107-systems/l3xz-cad/cad/upper_deck/emergency_stop_TC-9219036.step

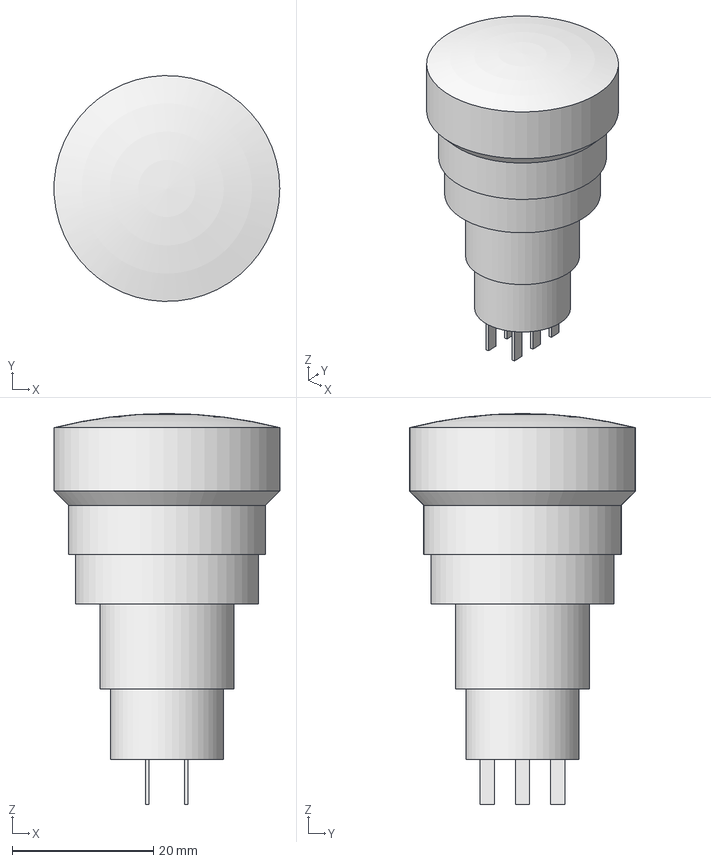
[picture p15: CAD file, 2023-01-18]
cad/upper_deck/emergency_stop_TC-9219036.step
32.0 x 32.0 x 55.4 mm
