107-systems/l3xz-cad/cad/body-bottom-middle-bracket-holes.dxf

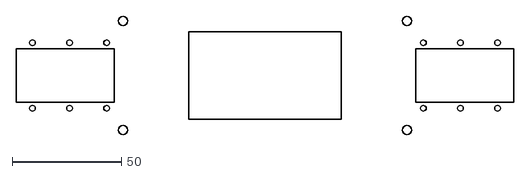
[picture p16: CAD file, 2022-04-17]
cad/body-bottom-middle-bracket-holes.dxf
228.0 x 54.3
