107-systems/l3xz-cad/cad/upper_deck/Adafruit_Neopixel.step

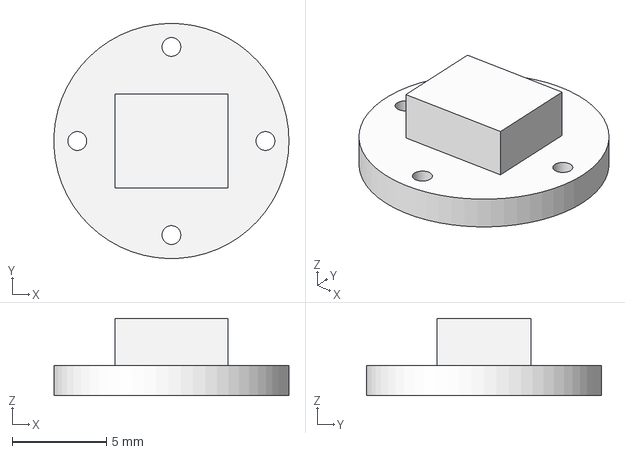
[picture p17: CAD file, 2022-05-29]
cad/upper_deck/Adafruit_Neopixel.step
12.5 x 12.5 x 4.10 mm
