107-systems/l3xz-cad/cad/middle-bracket.step

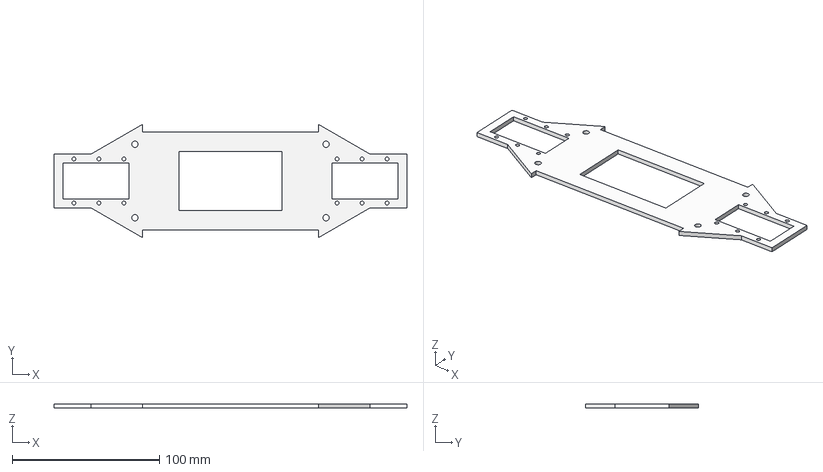
[picture p18: CAD file, 2022-04-17]
cad/middle-bracket.step
240.0 x 76.8 x 3.00 mm
