107-systems/l3xz-cad/cad/upper_deck/Scanse_Sweep_Adapter.step

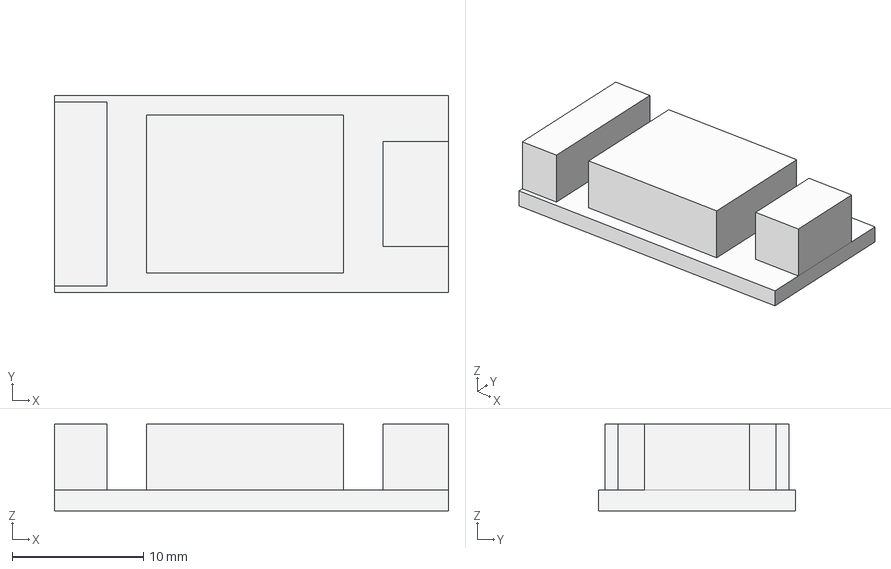
[picture p19: CAD file, 2022-05-29]
cad/upper_deck/Scanse_Sweep_Adapter.step
30.0 x 15.0 x 6.60 mm
