107-systems/l3xz-cad/cad/switch_mount.step

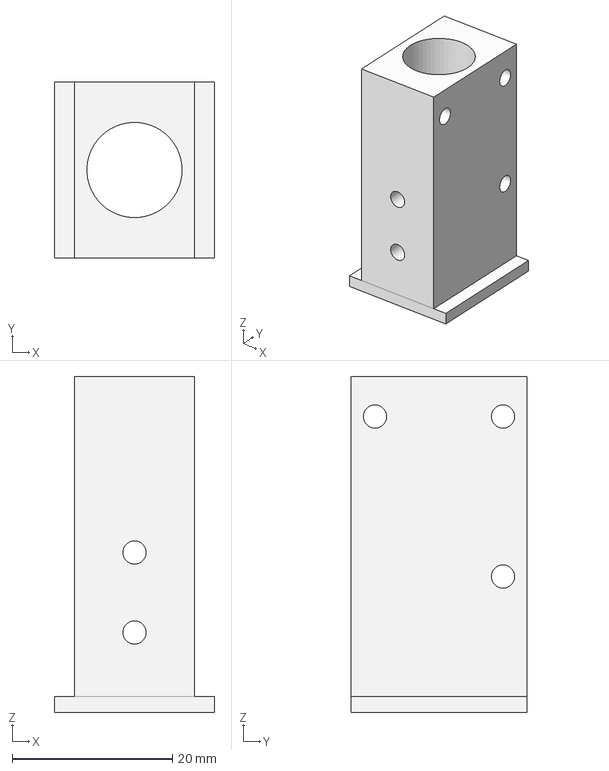
[picture p20: CAD file, 2022-04-17]
cad/switch_mount.step
20.0 x 22.0 x 42.0 mm
