107-systems/l3xz-cad/cad/upper_deck/Scanse_Sweep.step

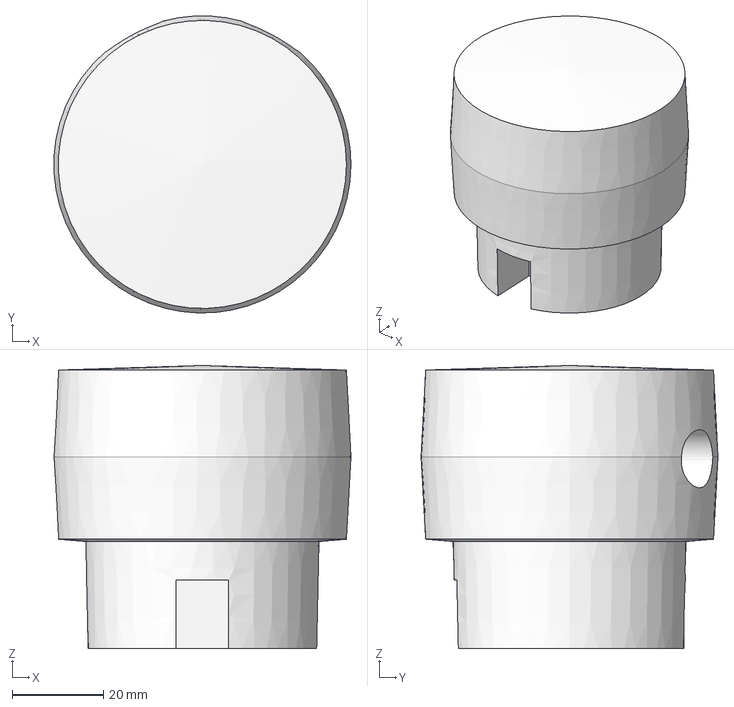
[picture p21: CAD file, 2022-04-17]
cad/upper_deck/Scanse_Sweep.step
65.0 x 64.9 x 61.9 mm
