107-systems/l3xz-cad/cad/body-bottom-back-bracket-base.dxf

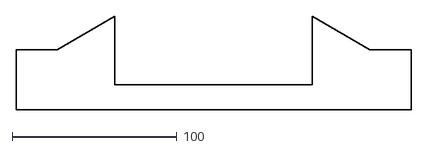
[picture p22: CAD file, 2022-04-17]
cad/body-bottom-back-bracket-base.dxf
240.0 x 56.6
