107-systems/l3xz-cad/cad/front-bracket.step

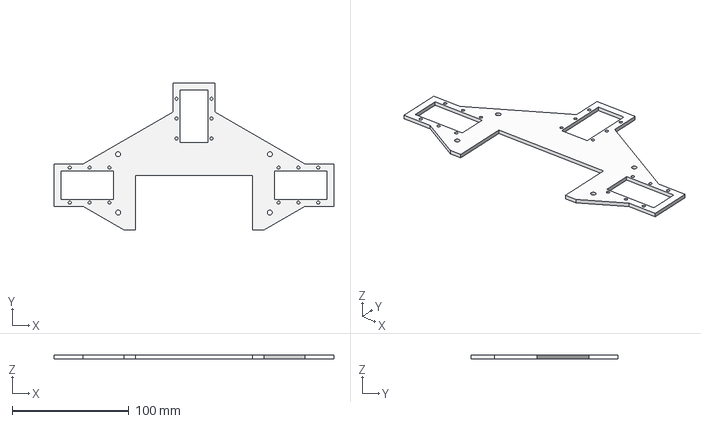
[picture p23: CAD file, 2022-04-17]
cad/front-bracket.step
240.0 x 125.9 x 3.00 mm
