107-systems/l3xz-cad/cad/body-bottom-top-holes.dxf

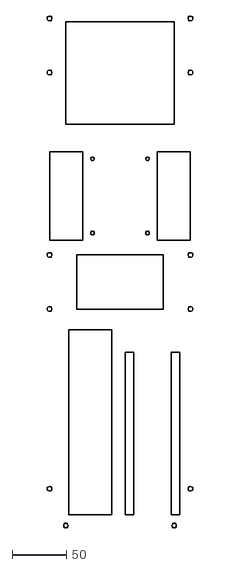
[picture p24: CAD file, 2022-04-17]
cad/body-bottom-top-holes.dxf
134.3 x 472.7
