107-systems/l3xz-cad/cad/body-bottom-top-base.dxf

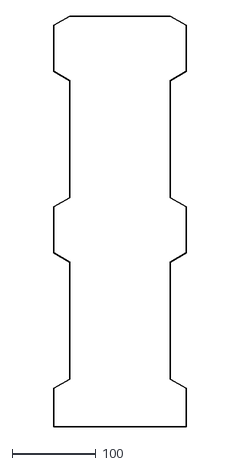
[picture p25: CAD file, 2022-04-17]
cad/body-bottom-top-base.dxf
158.0 x 490.2
