107-systems/l3xz-cad/cad/body-bottom-back-bracket-holes.dxf

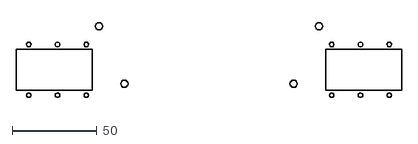
[picture p26: CAD file, 2022-04-17]
cad/body-bottom-back-bracket-holes.dxf
228.0 x 44.3
