107-systems/l3xz-cad/cad/0H1650A.step

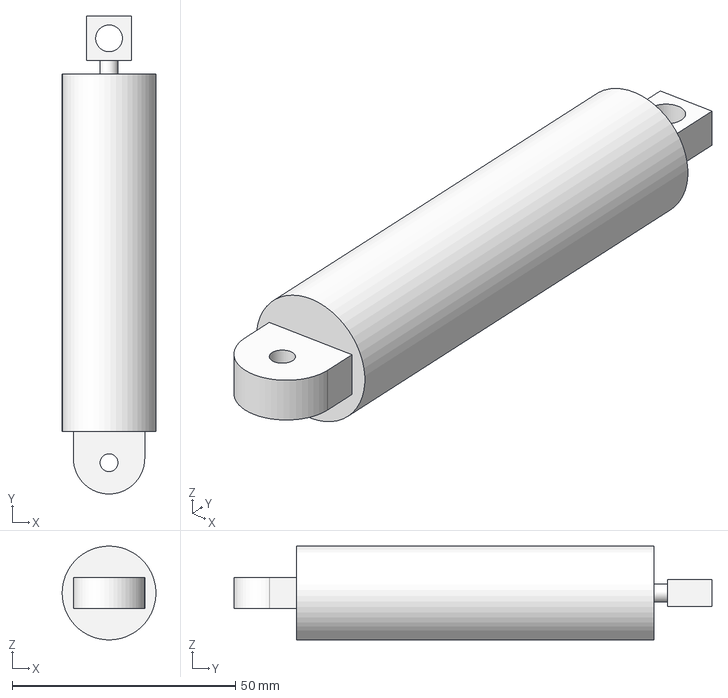
[picture p27: CAD file, 2022-04-17]
cad/0H1650A.step
21.0 x 107.0 x 21.0 mm
