107-systems/l3xz-cad/cad/back-bracket.step

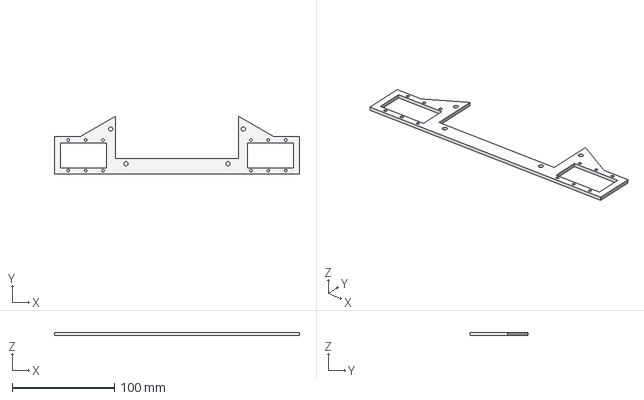
[picture p28: CAD file, 2022-04-17]
cad/back-bracket.step
240.0 x 56.6 x 3.00 mm
