107-systems/l3xz-cad/cad/body-bottom-middle-bracket-base.dxf

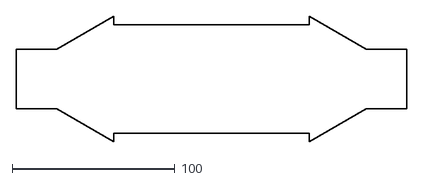
[picture p29: CAD file, 2022-04-17]
cad/body-bottom-middle-bracket-base.dxf
240.0 x 76.8
