107-systems/l3xz-cad/cad/body-bottom-holes.dxf

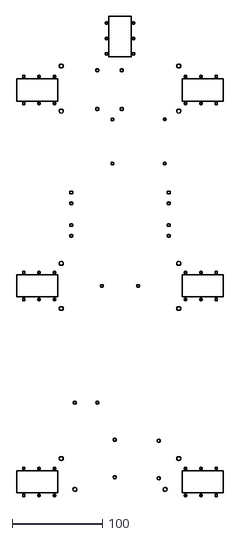
[picture p30: CAD file, 2022-03-28]
cad/body-bottom-holes.dxf
228.0 x 531.5
