107-systems/l3xz-cad/cad/l3xz.FCStd

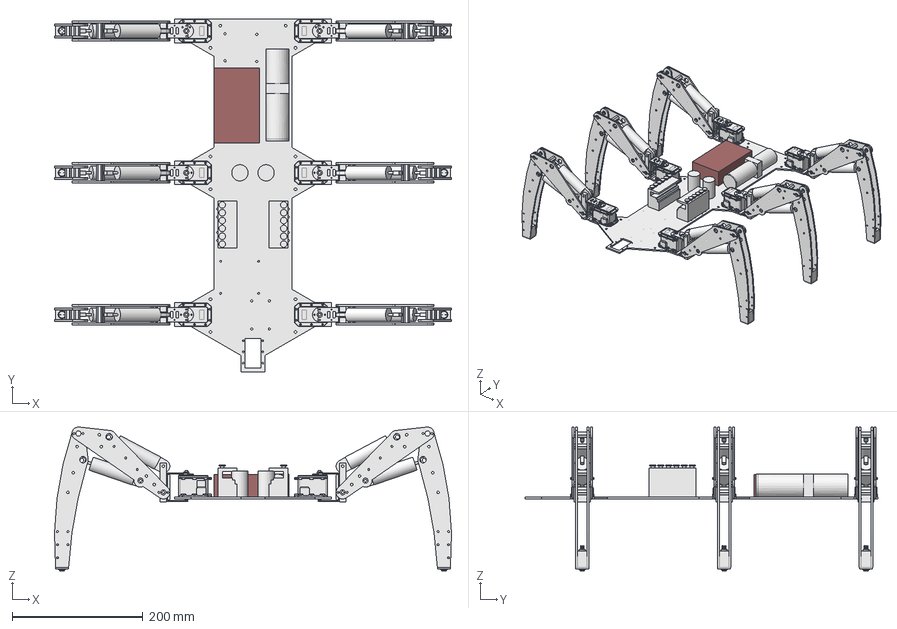
[picture p31: CAD file, 2022-03-28]
cad/l3xz.FCStd
607.1 x 539.4 x 220.2 mm
leg007
leg008
leg009
leg010
leg011
leg012
battery
filter1
filter002
