107-systems/l3xz-cad/cad/body-bottom.step

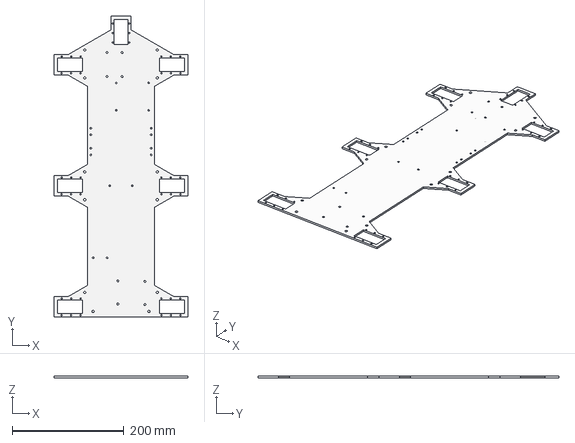
[picture p32: CAD file, 2022-03-28]
cad/body-bottom.step
240.0 x 539.4 x 3.00 mm
