107-systems/l3xz-cad/cad/tibia.step

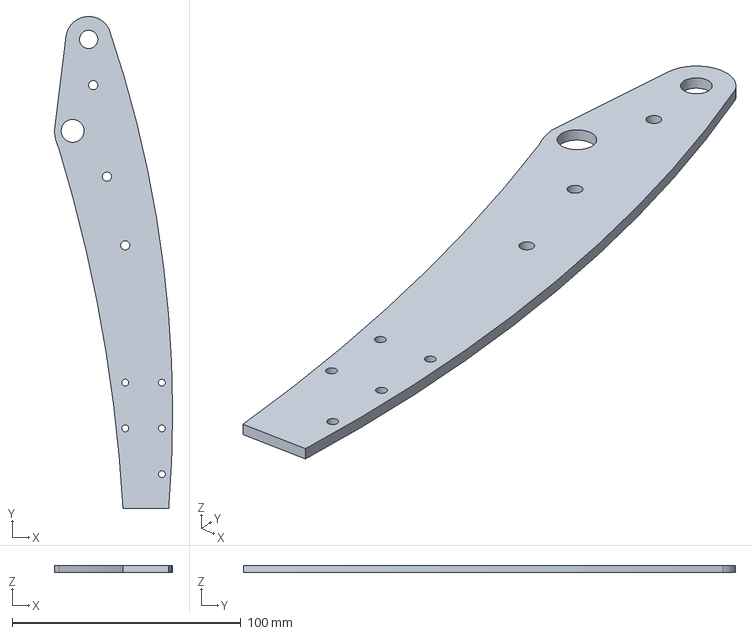
[picture p33: CAD file, 2022-03-28]
cad/tibia.step
51.7 x 215.0 x 3.00 mm
