107-systems/l3xz-cad/cad/body-bottom-base.dxf

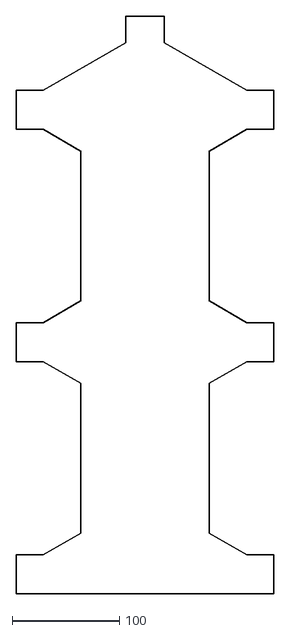
[picture p34: CAD file, 2022-03-28]
cad/body-bottom-base.dxf
240.0 x 539.4
