107-systems/l3xz-cad/cad/FR07-H101.stp

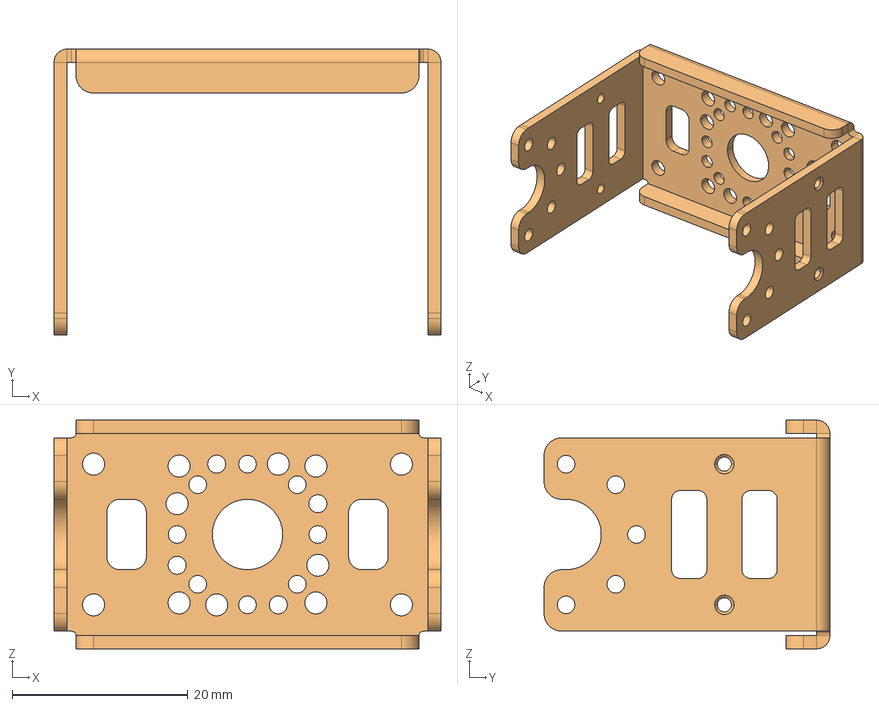
[picture p35: CAD file, 2022-03-28]
cad/FR07-H101.stp
44.0 x 32.5 x 26.0 mm
