107-systems/l3xz-cad/cad/0H108A.step

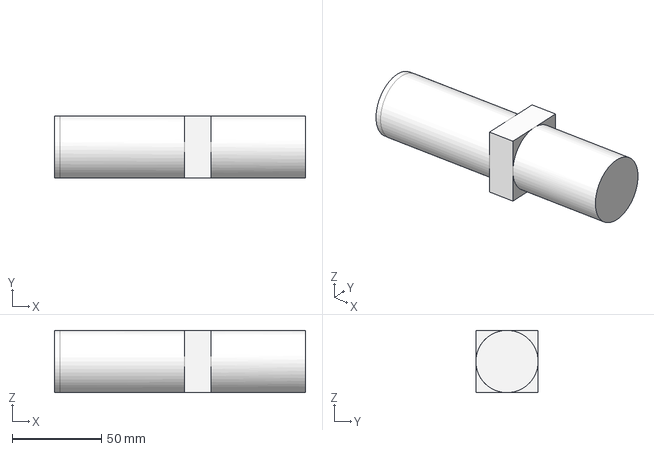
[picture p36: CAD file, 2022-03-28]
cad/0H108A.step
141.0 x 35.0 x 35.0 mm
