107-systems/l3xz-cad/cad/leg.step

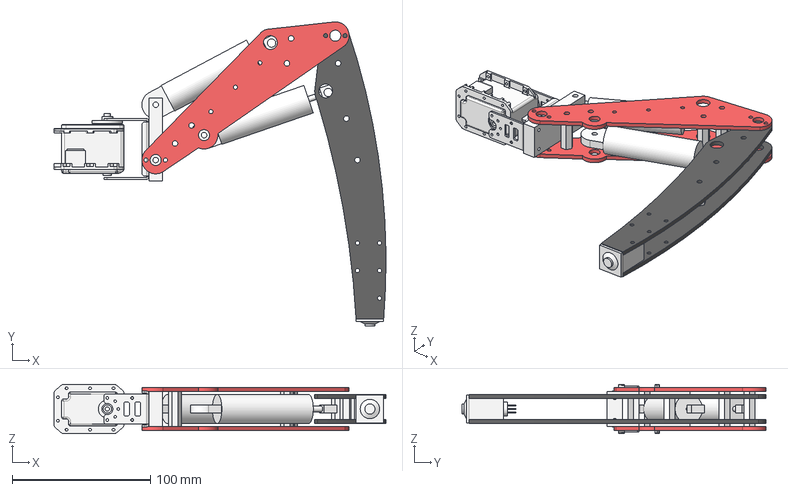
[picture p37: CAD file, 2022-03-28]
cad/leg.step
240.3 x 220.2 x 35.6 mm
femur01
dynamixel_joint002
FR07-H101
DC07_A_DUMMY_AL
0H1650A
0H1650A001
tibia01
tibia02
LAS4GQH-11_S
femur02
switch_mount
