107-systems/l3xz-cad/cad/femur.step

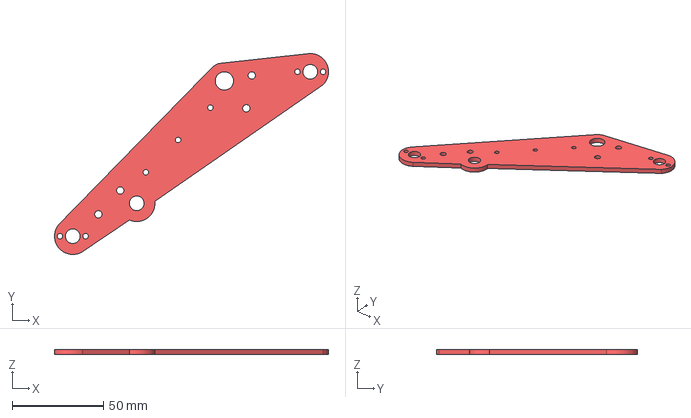
[picture p38: CAD file, 2022-03-28]
cad/femur.step
150.0 x 110.0 x 3.00 mm
