107-systems/l3xz-cad/cad/0H506A.step

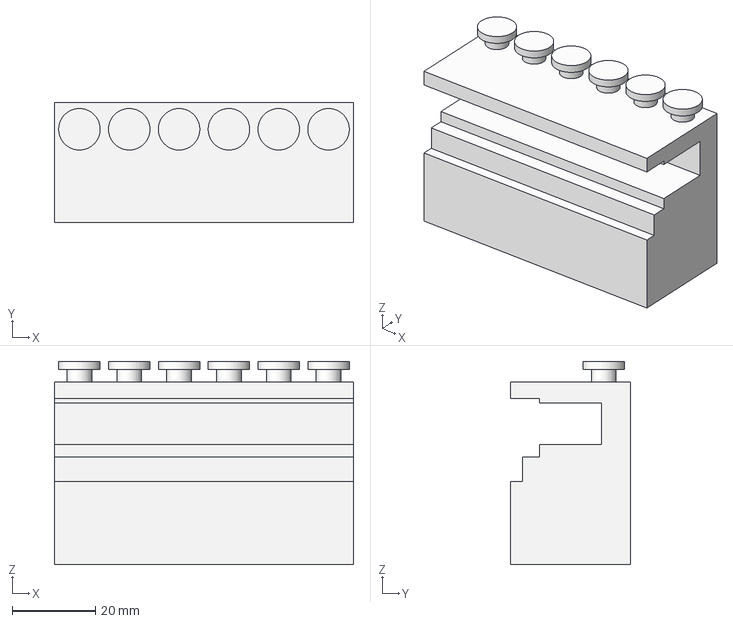
[picture p39: CAD file, 2022-03-28]
cad/0H506A.step
72.0 x 29.0 x 49.0 mm
