107-systems/l3xz-cad/cad/LAS4GQH-11_S.step

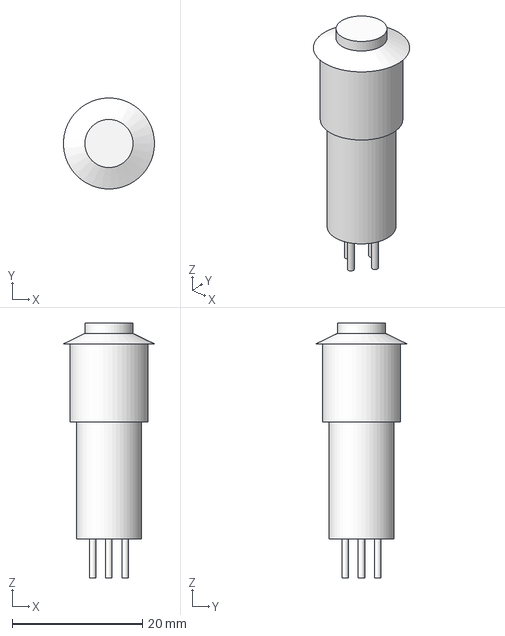
[picture p40: CAD file, 2022-03-28]
cad/LAS4GQH-11_S.step
14.0 x 14.0 x 39.2 mm
