107-systems/l3xz-cad/cad/MX-28AT_AR.stp

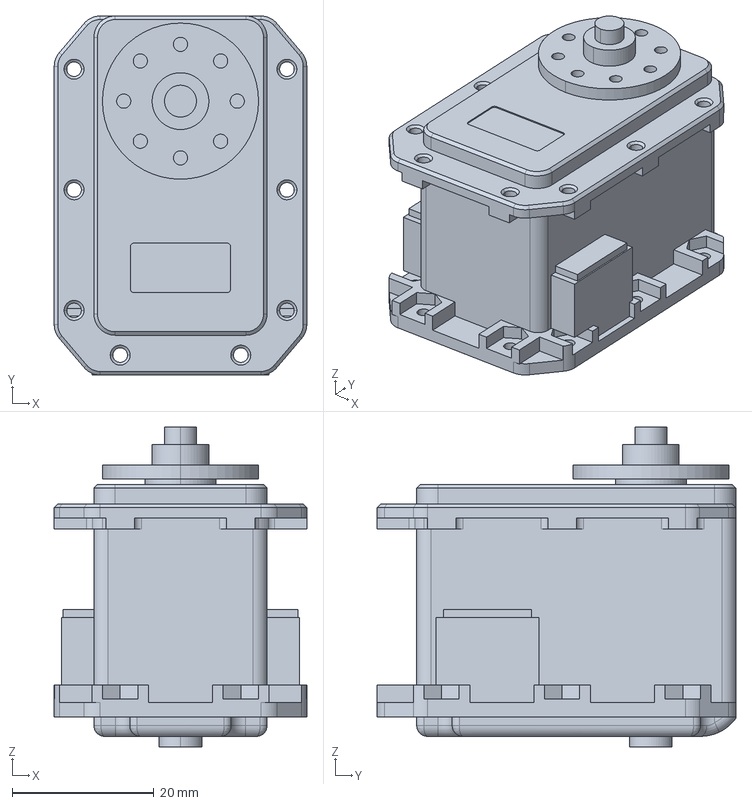
[picture p41: CAD file, 2022-03-28]
cad/MX-28AT_AR.stp
35.6 x 50.6 x 45.1 mm
